ochin-space/ochin-CM4/3d/Covers turrets and extractors/ochin_mount.jpg

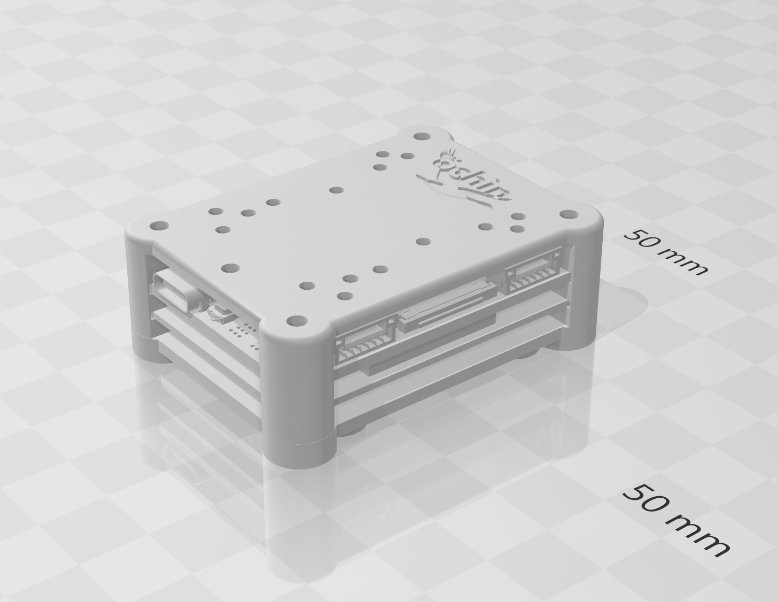
3d/Covers turrets and extractors/ochin_mount.jpg
