ochin-space/ochin-CM4/3d/EasyStar ii_IMX219_mount/IMX219_mount_2.png

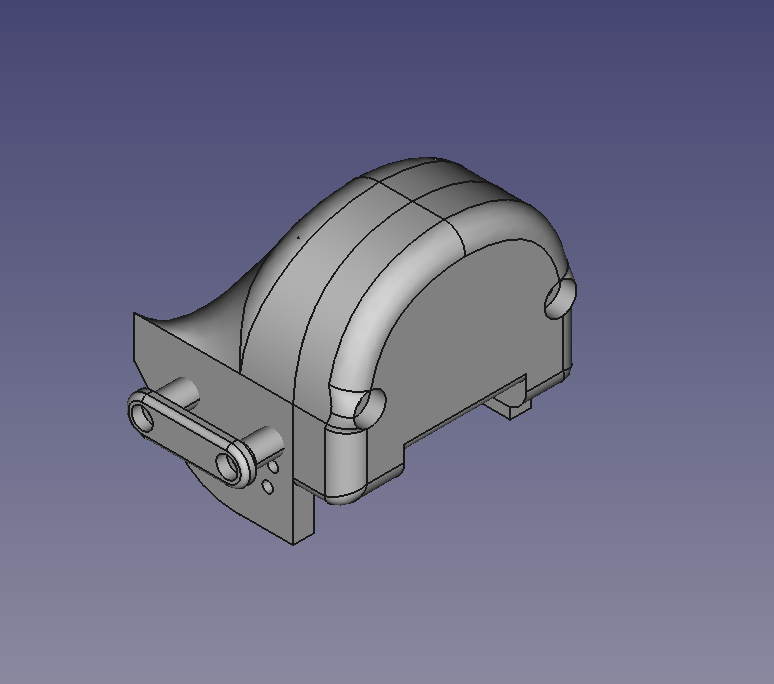
3d/EasyStar ii_IMX219_mount/IMX219_mount_2.png
