ochin-space/ochin-CM4/3d/ochin_cm4_plate_mount/ochin_cm4_plate_mount_2.png

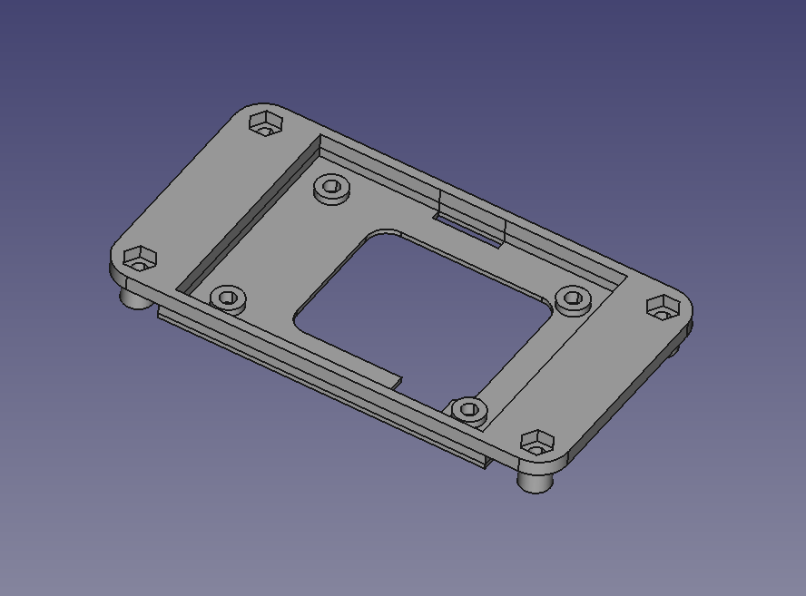
3d/ochin_cm4_plate_mount/ochin_cm4_plate_mount_2.png
