ochin-space/ochin-CM4/3d/opchin_cm4/ochin_cm4.png

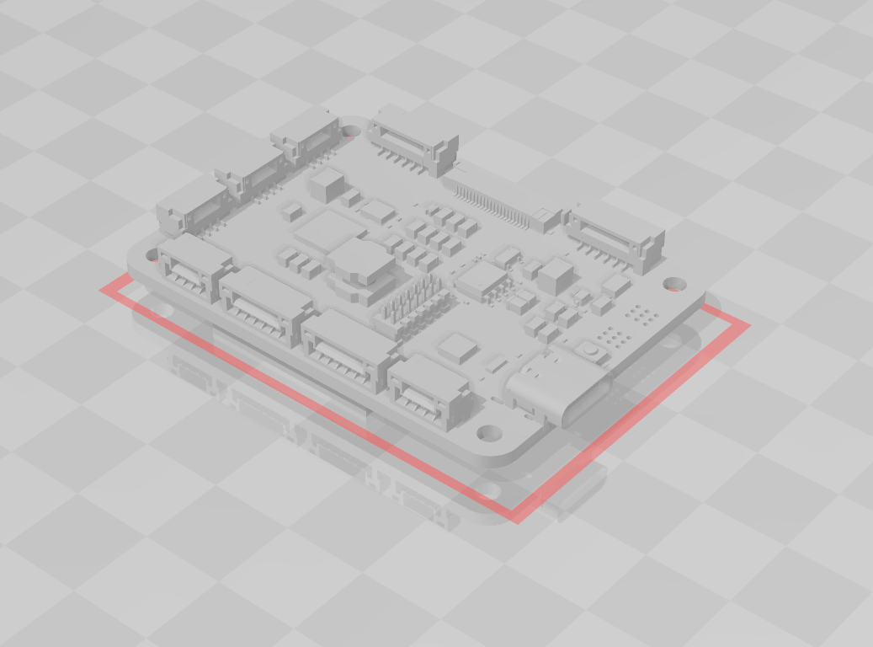
3d/opchin_cm4/ochin_cm4.png
