ochin-space/ochin-CM4/images/IMG_20210730_141659.jpg

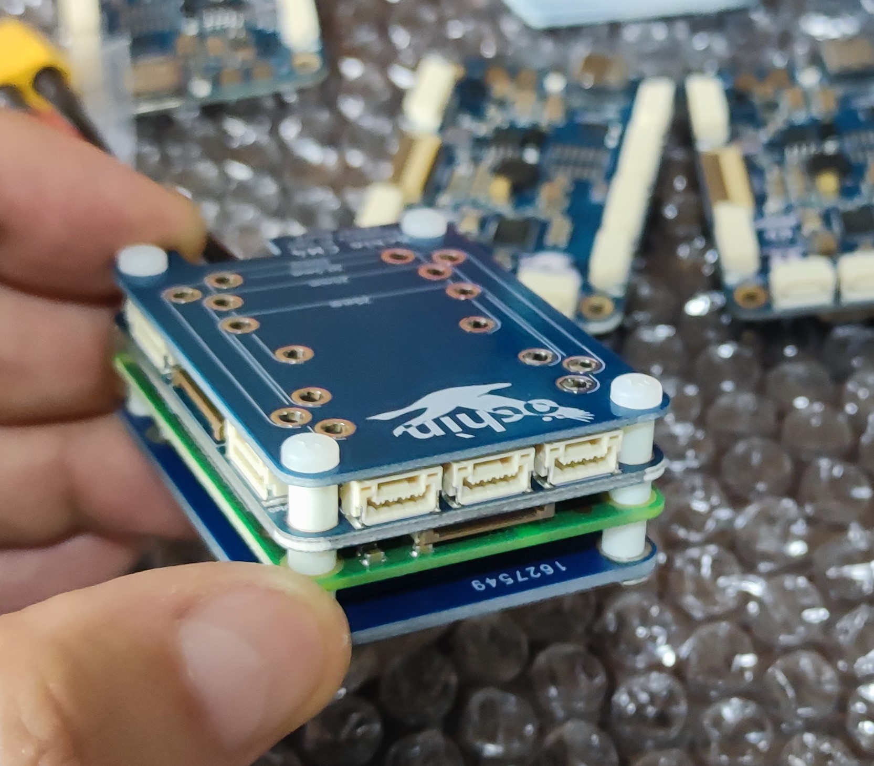
images/IMG_20210730_141659.jpg
