ochin-space/ochin-CM4/images/IMG_20210819_091649.jpg

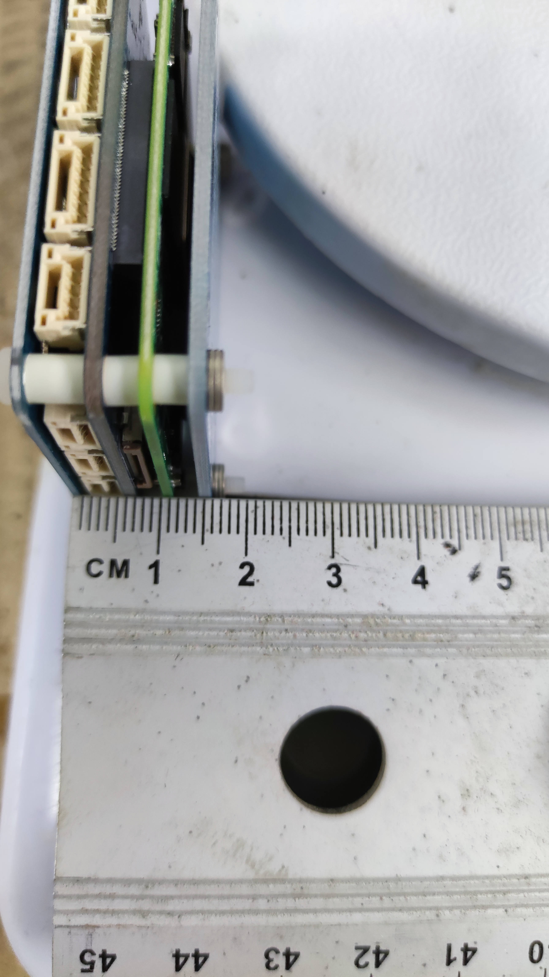
images/IMG_20210819_091649.jpg
