ochin-space/ochin-CM4/images/IMG_20210819_091912.jpg

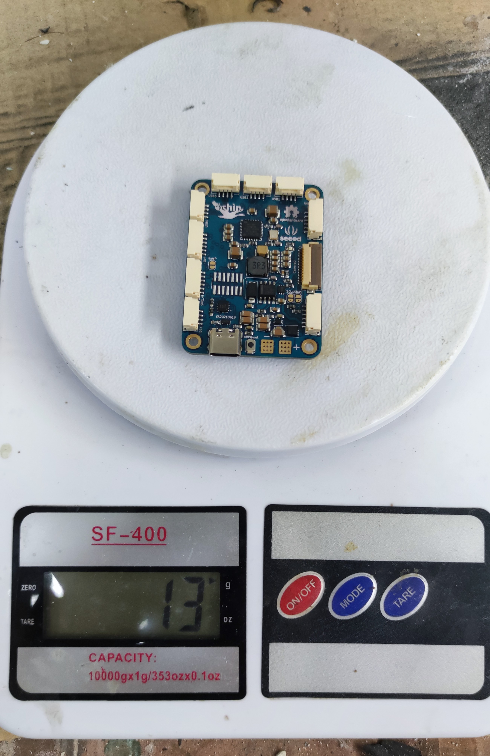
images/IMG_20210819_091912.jpg
