ochin-space/ochin-CM4/images/IMG_20210819_091925.jpg

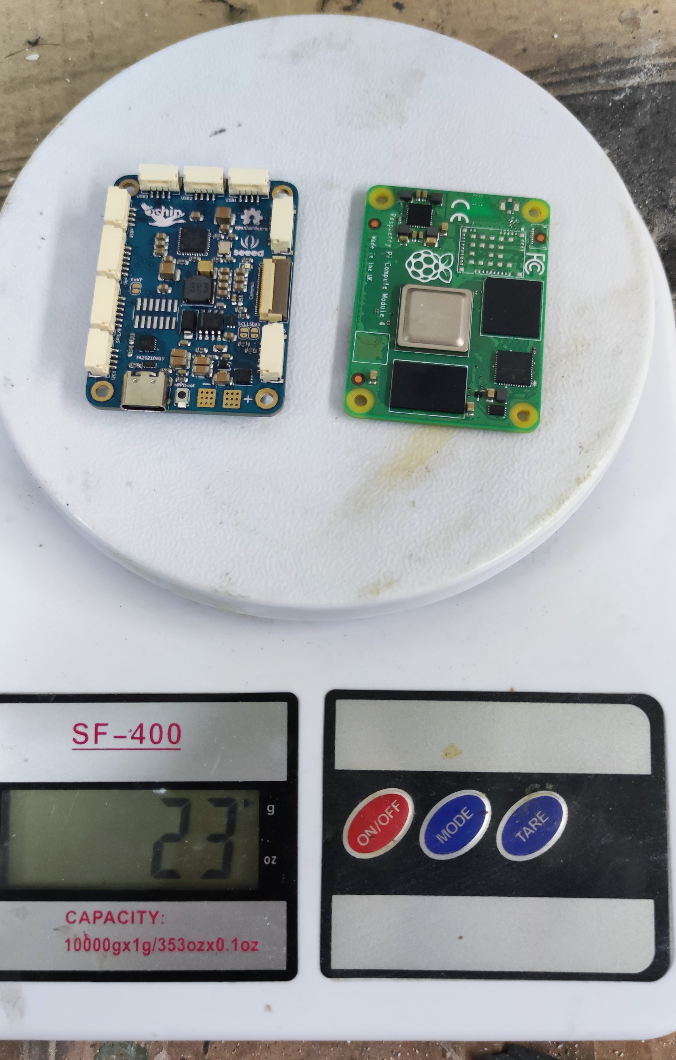
images/IMG_20210819_091925.jpg
