ochin-space/ochin-CM4/images/IMG_20220202_005142.jpg

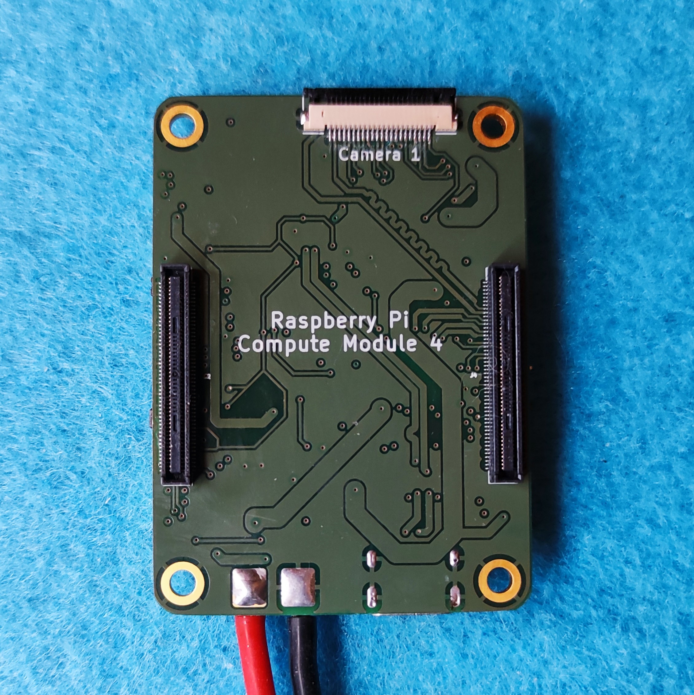
images/IMG_20220202_005142.jpg
