ochin-space/ochin-CM4/images/Ochin_CM4_front.jpg

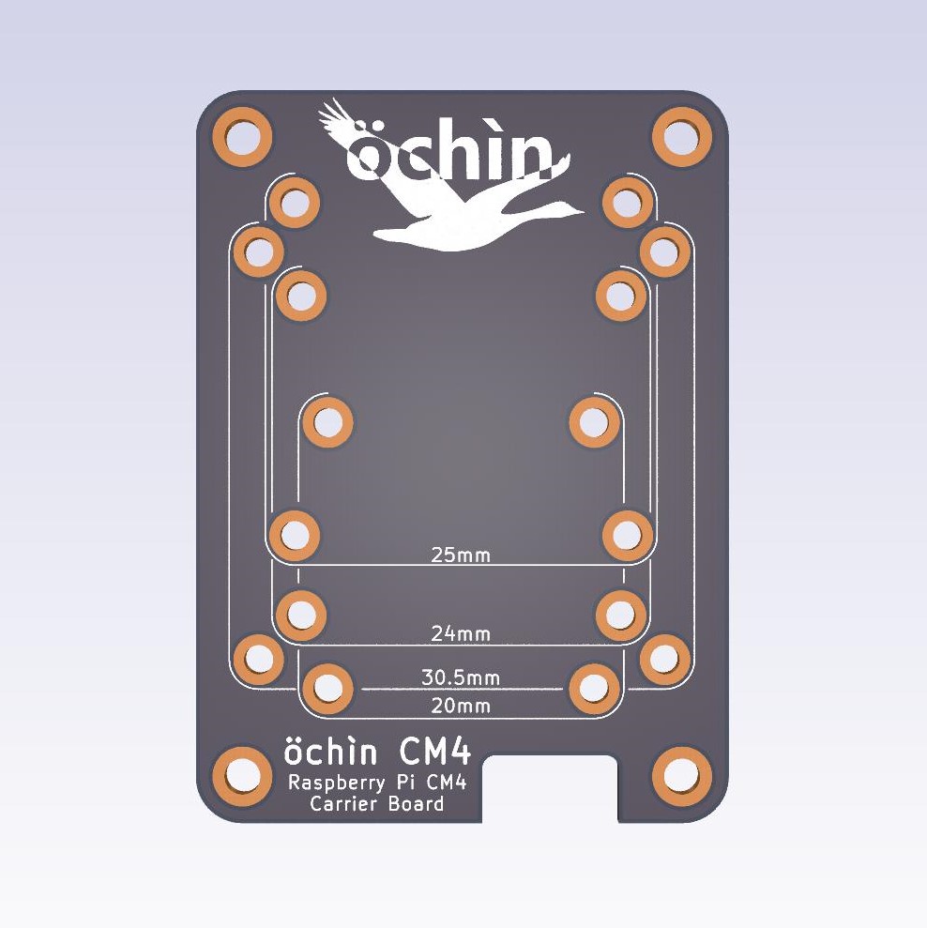
images/Ochin_CM4_front.jpg
