ochin-space/ochin-CM4/images/Ochin_CM4_top_.jpg

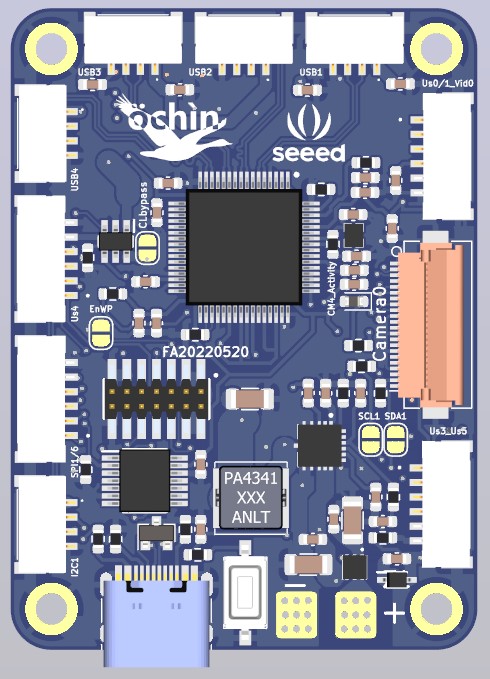
images/Ochin_CM4_top_.jpg
