ochin-space/ochin-CM4/images/OchinCM4_2.jpg

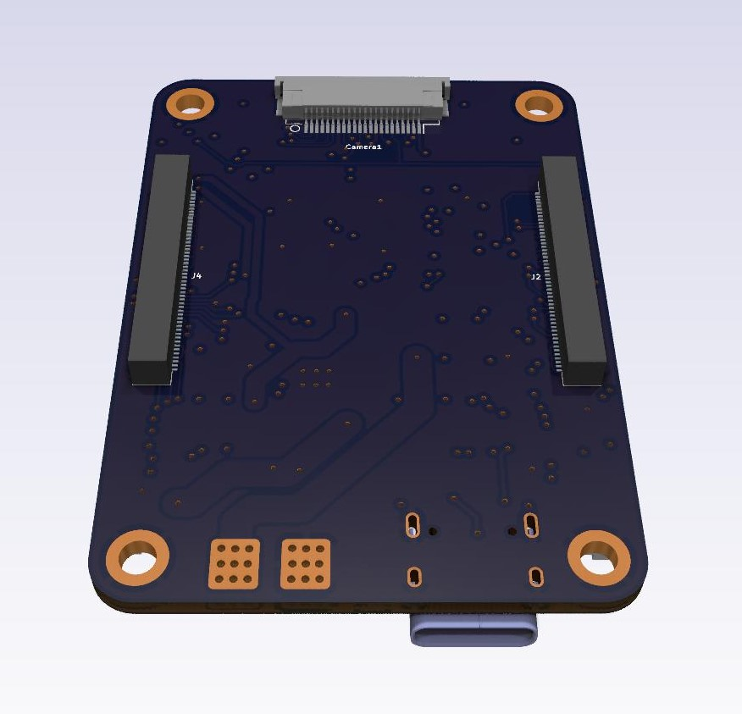
images/OchinCM4_2.jpg
