ochin-space/ochin-CM4/3d/Covers turrets and extractors/ochin_mount-topCover.stl

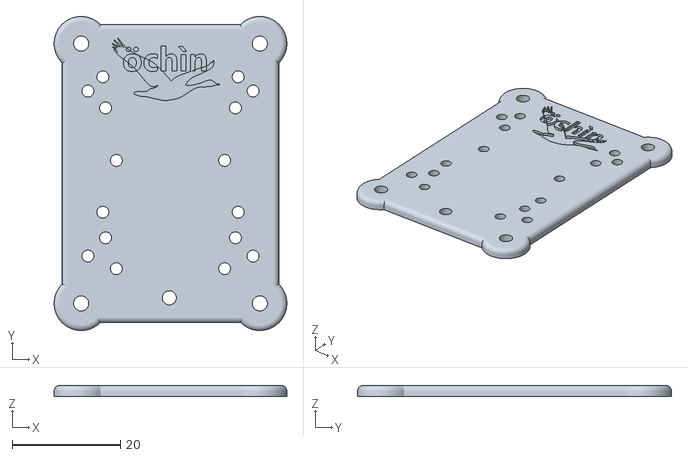
[picture p39: CAD file, 2022-03-25]
3d/Covers turrets and extractors/ochin_mount-topCover.stl
43.0 x 58.0 x 2.00
