ochin-space/ochin-CM4/3d/EasyStar ii_IMX219_mount/EasyStar_camera_mount_front.stl

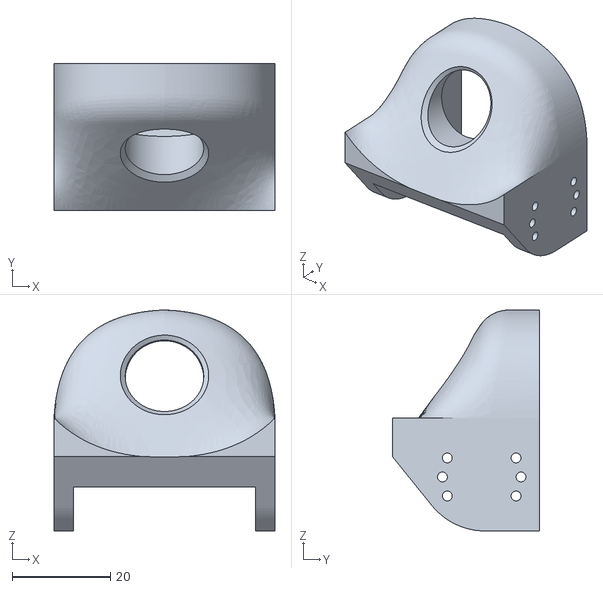
[picture p40: CAD file, 2021-09-21]
3d/EasyStar ii_IMX219_mount/EasyStar_camera_mount_front.stl
45.0 x 30.0 x 45.0
