ochin-space/ochin-CM4/3d/Covers turrets and extractors/ochin_mount-botCover.stl

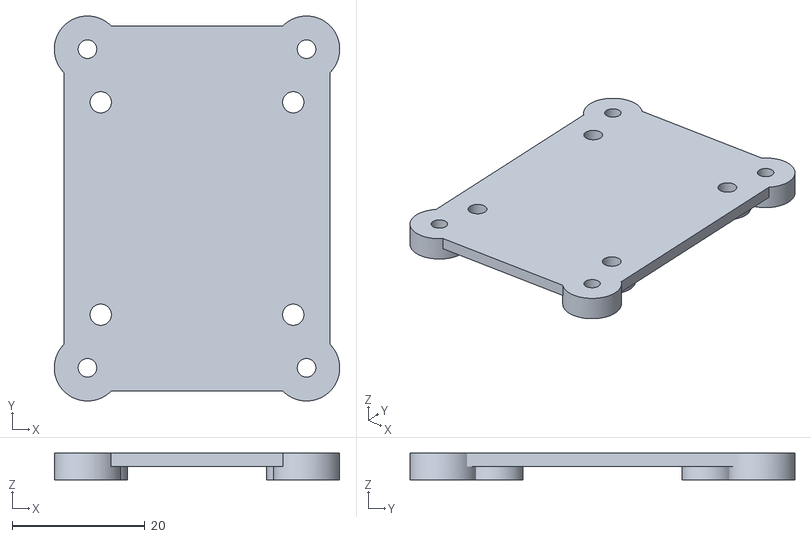
[picture p41: CAD file, 2022-03-25]
3d/Covers turrets and extractors/ochin_mount-botCover.stl
43.0 x 58.0 x 4.00
