ochin-space/ochin-CM4/3d/camera microservo gimbal/ochin_plate.FCStd

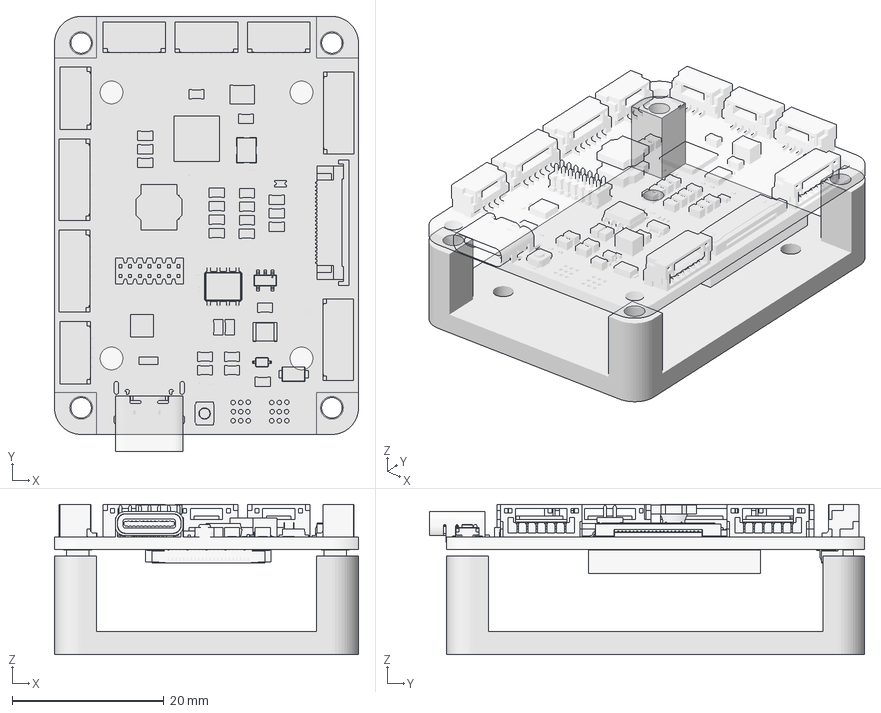
[picture p42: CAD file, 2022-09-01]
3d/camera microservo gimbal/ochin_plate.FCStd
40.0 x 57.3 x 19.8 mm
Bot Plate
ochin_CM4-Ochin
