ochin-space/ochin-CM4/3d/camera microservo gimbal/ochin_plate-Bot Plate.stl

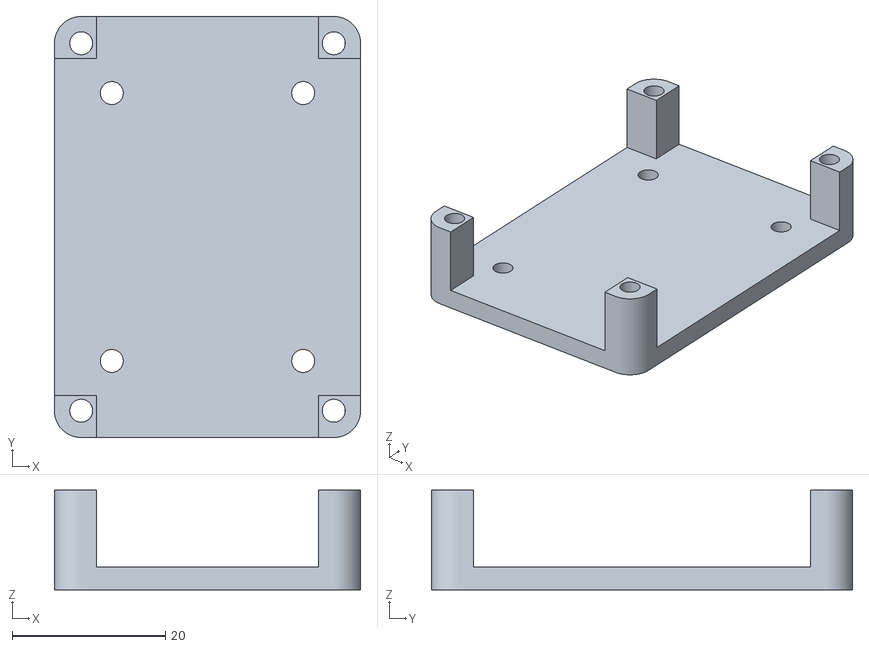
[picture p43: CAD file, 2022-09-01]
3d/camera microservo gimbal/ochin_plate-Bot Plate.stl
40.0 x 55.0 x 13.0
