ochin-space/ochin-CM4/öchìn CM4 - Quick Start Flashing Guide.png

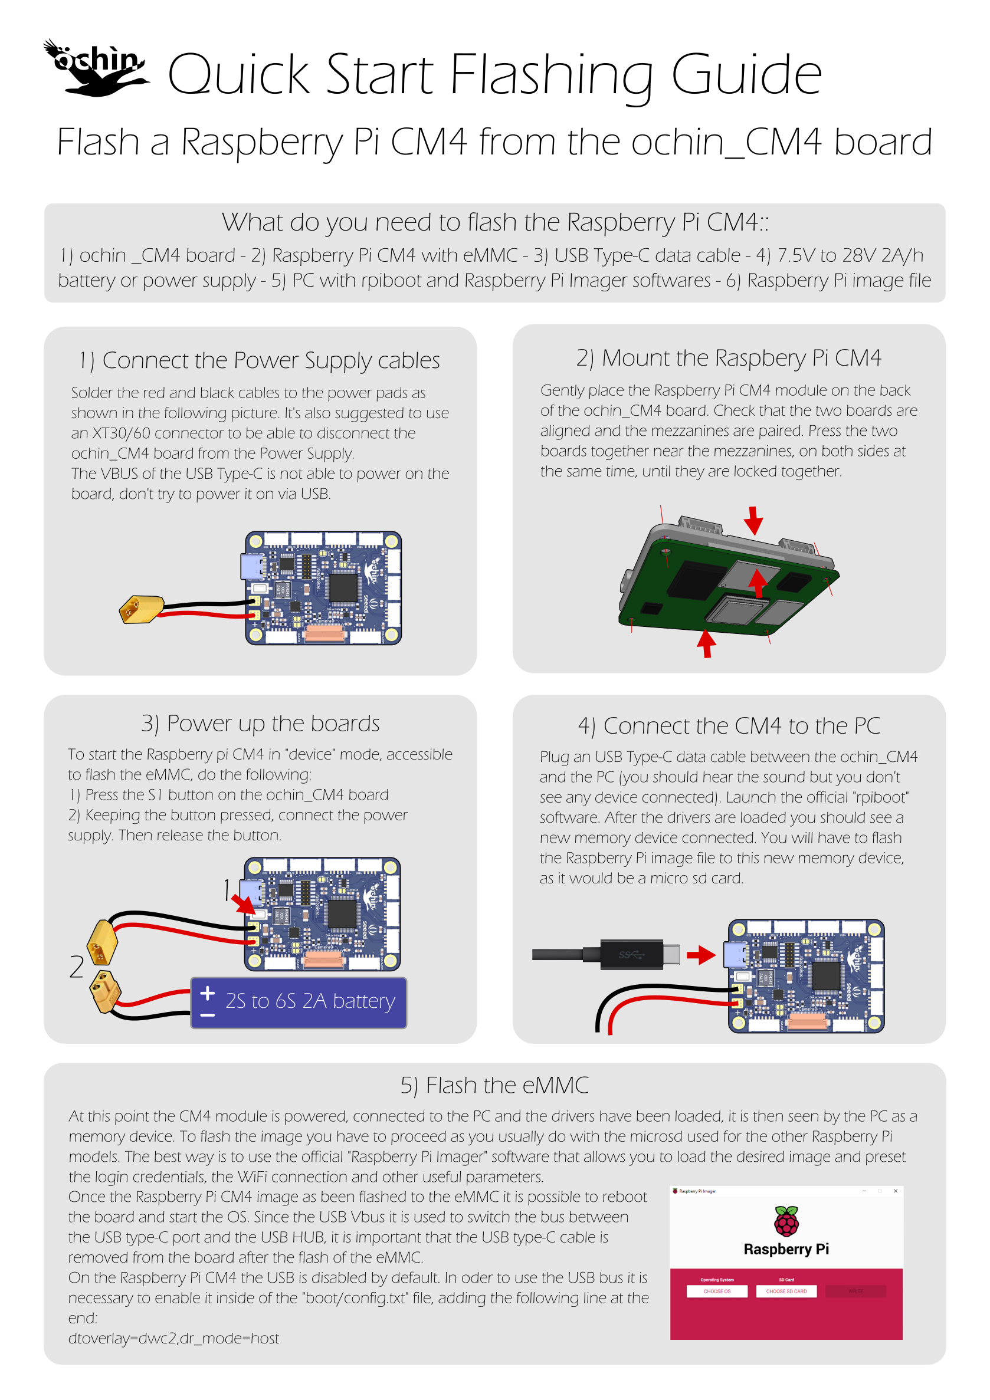
öchìn CM4 - Quick Start Flashing Guide.png
